maynej/Escornabot-Singularis/Imatges/photo_2024-10-26_23-49-39.jpg

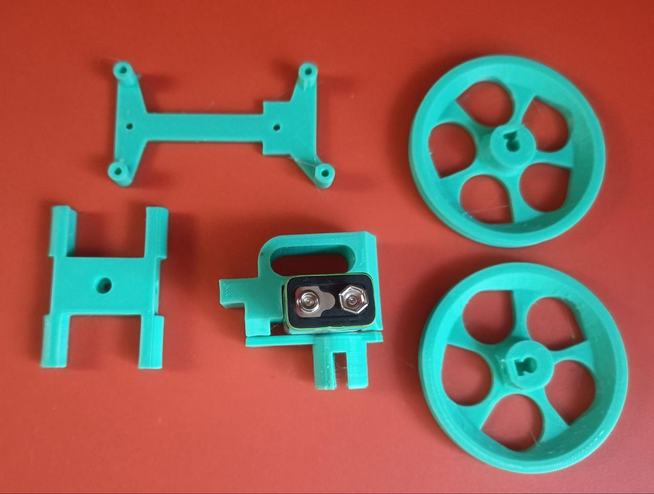
Imatges/photo_2024-10-26_23-49-39.jpg
